echopen-foundation/echolab_box/docs/img/20190922_094147.jpg

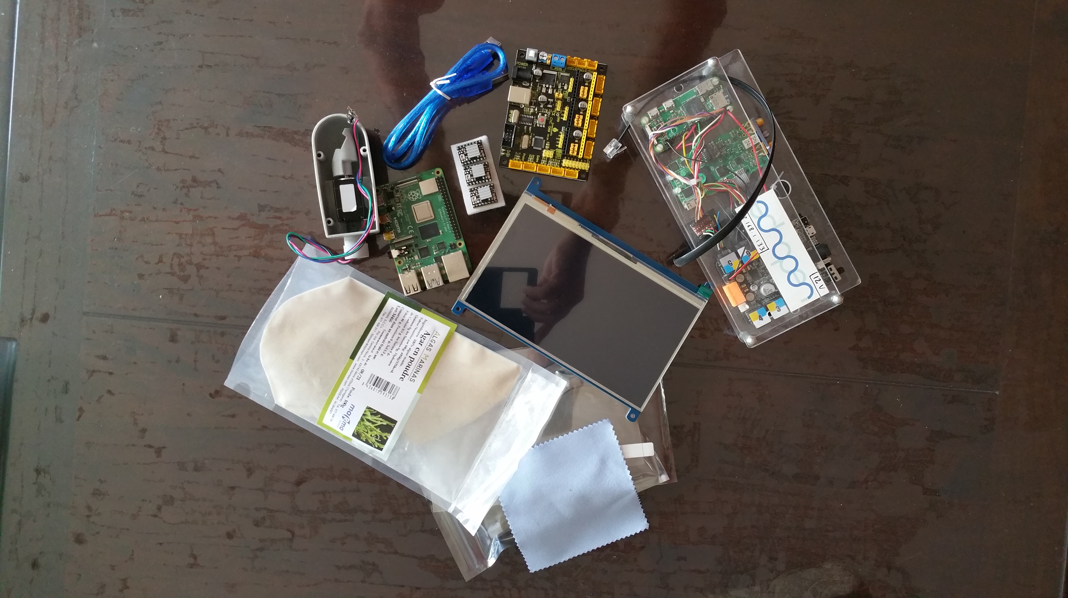
docs/img/20190922_094147.jpg
