echopen-foundation/echolab_box/docs/img/20190924_202057_2.jpg

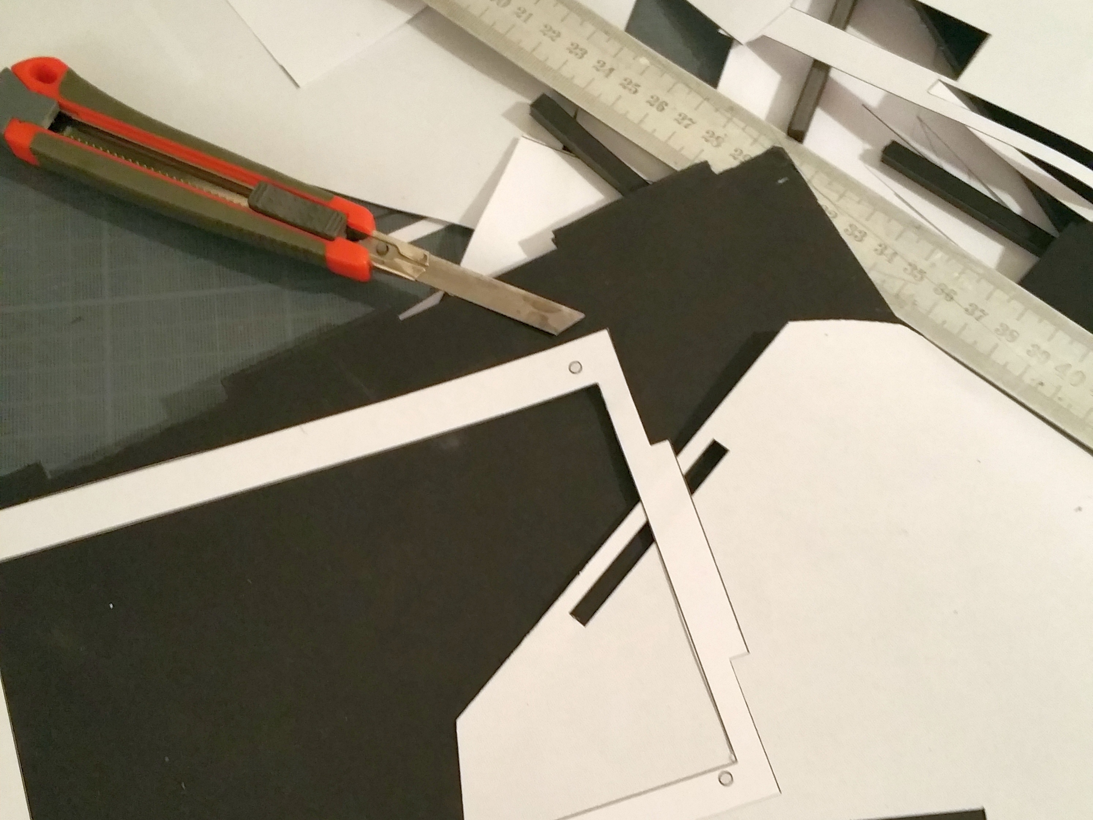
docs/img/20190924_202057_2.jpg
