echopen-foundation/echolab_box/docs/img/20190924_202208.jpg

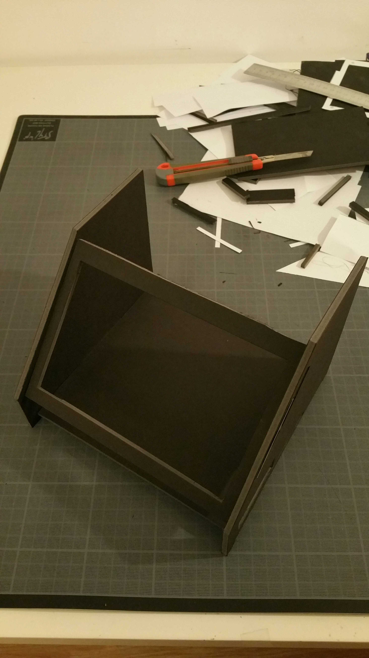
docs/img/20190924_202208.jpg
