echopen-foundation/echolab_box/docs/img/20190924_202229.jpg

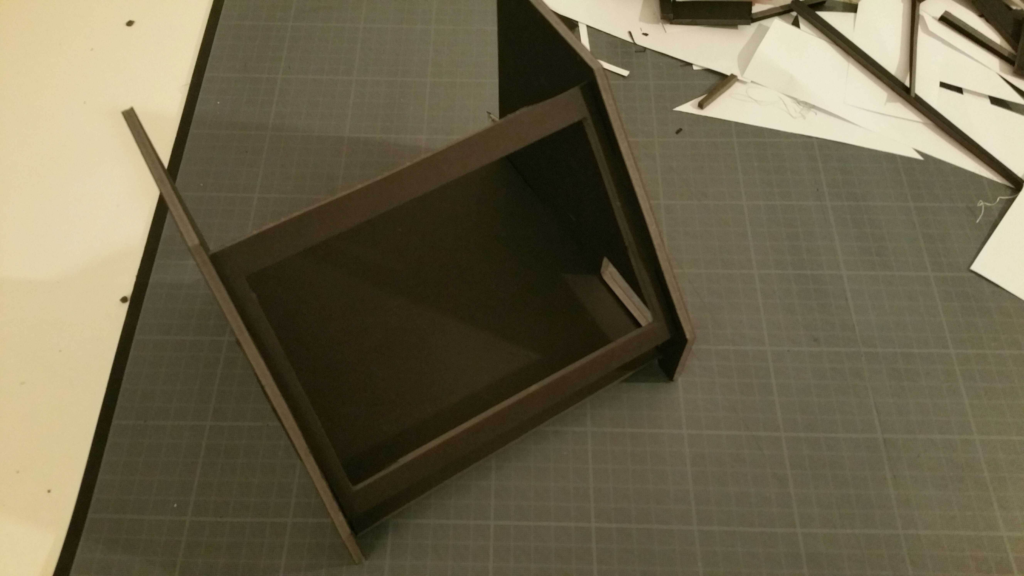
docs/img/20190924_202229.jpg
