echopen-foundation/echolab_box/docs/img/20190930_002303.jpg

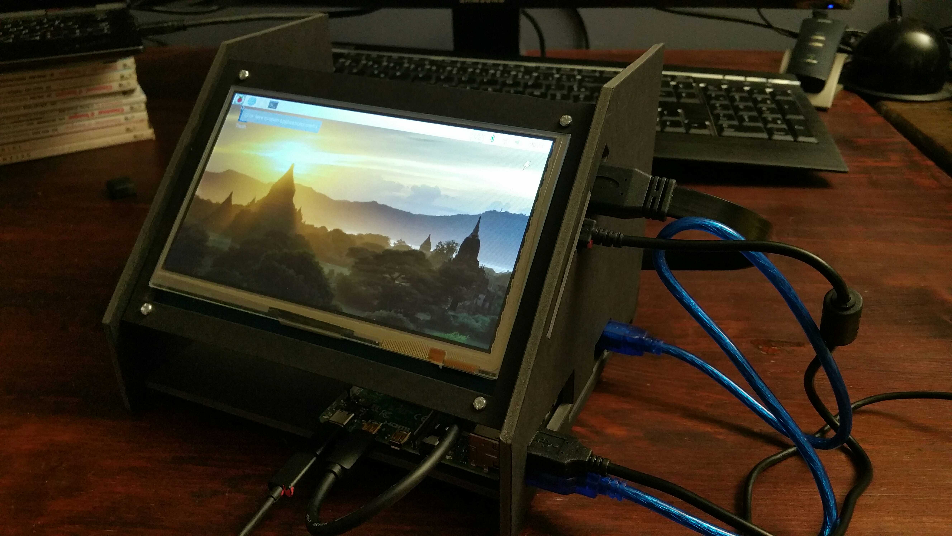
docs/img/20190930_002303.jpg
