echopen-foundation/echolab_box/docs/img/20190930_002329.jpg

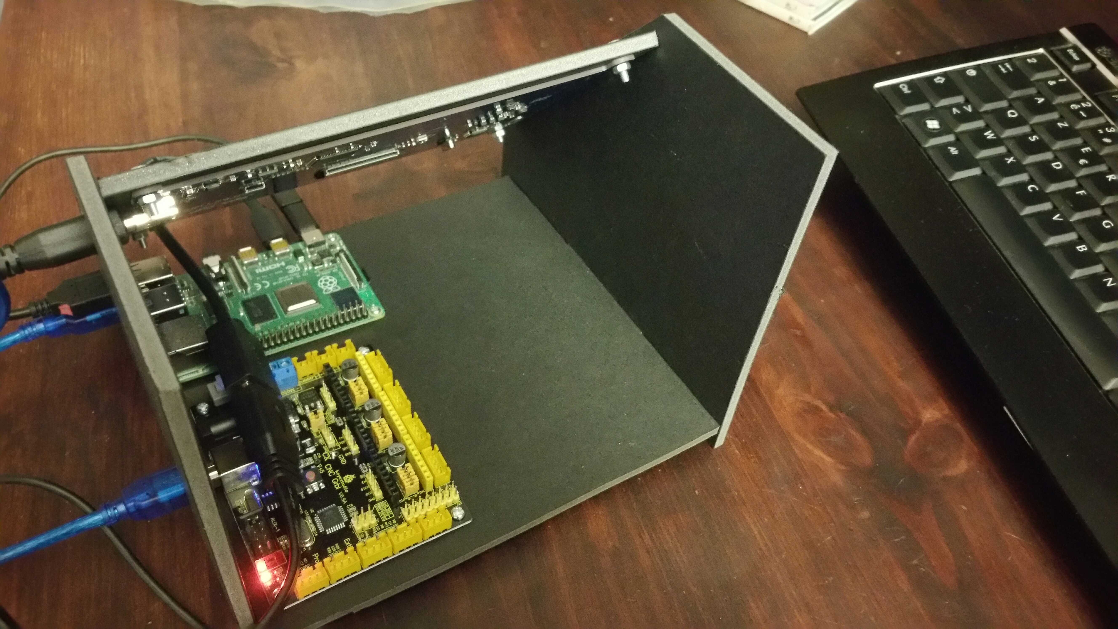
docs/img/20190930_002329.jpg
