echopen-foundation/echolab_box/docs/img/20191001_092123.jpg

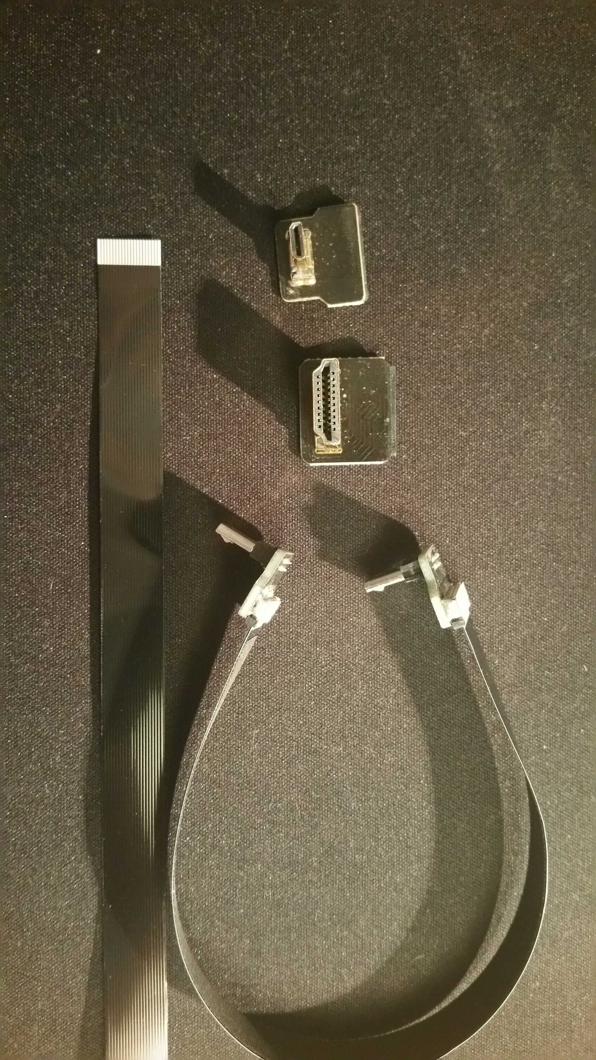
docs/img/20191001_092123.jpg
