echopen-foundation/echolab_box/docs/img/20191001_092209.jpg

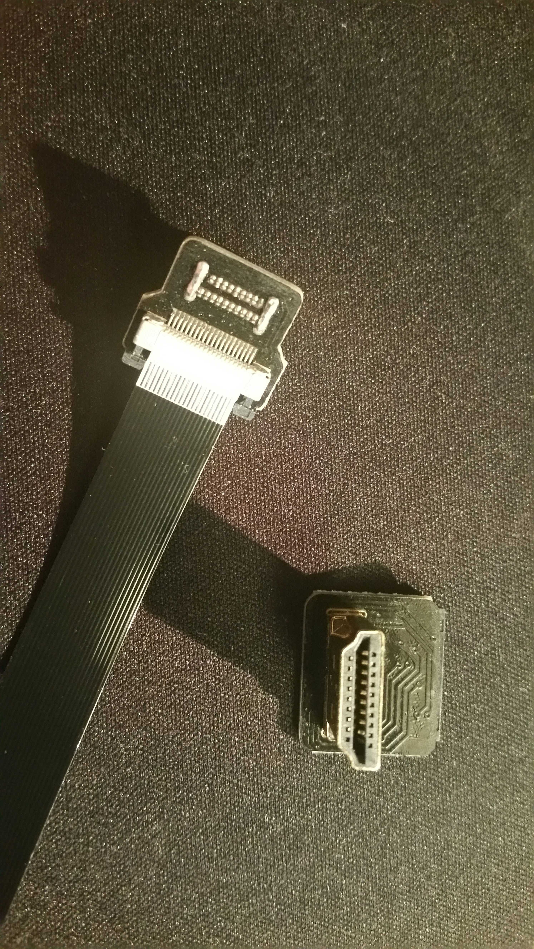
docs/img/20191001_092209.jpg
