echopen-foundation/echolab_box/docs/img/20191003_144745.jpg

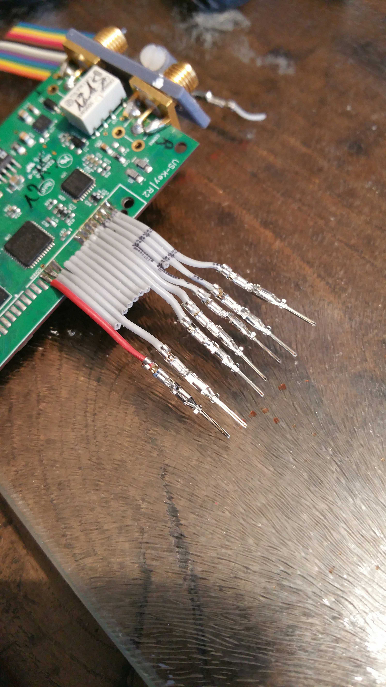
docs/img/20191003_144745.jpg
