echopen-foundation/echolab_box/docs/img/20191003_145241.jpg

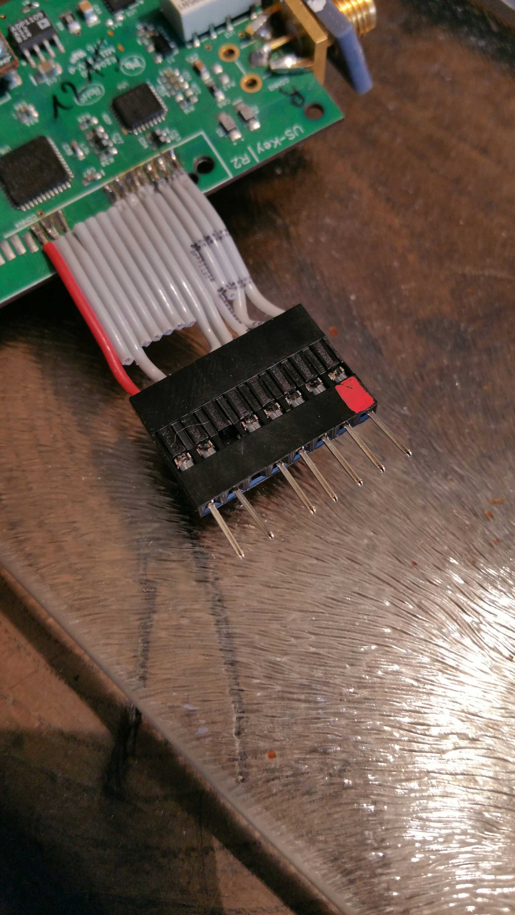
docs/img/20191003_145241.jpg
