echopen-foundation/echolab_box/docs/img/20191003_172906.jpg

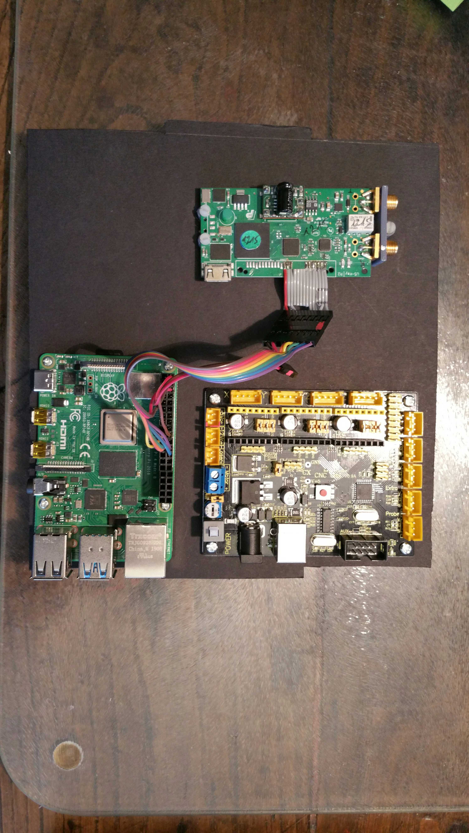
docs/img/20191003_172906.jpg
