echopen-foundation/echolab_box/docs/img/20191004_114859.jpg

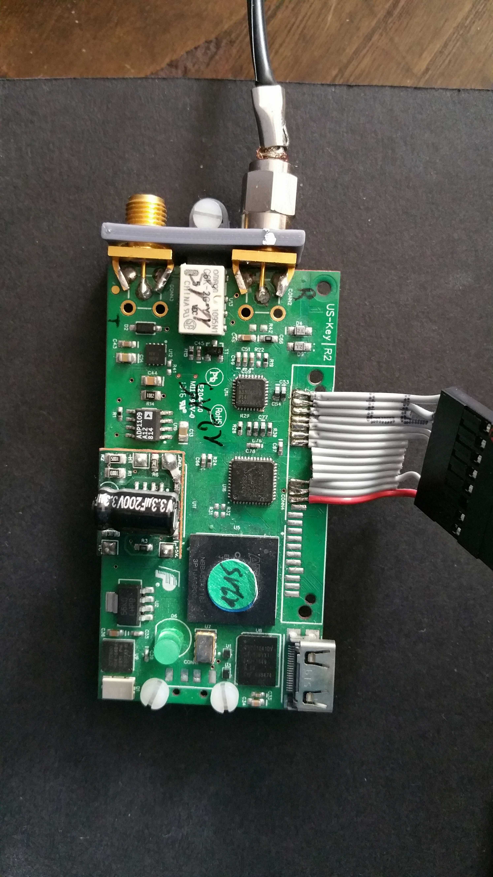
docs/img/20191004_114859.jpg
