echopen-foundation/echolab_box/docs/img/20191004_122543.jpg

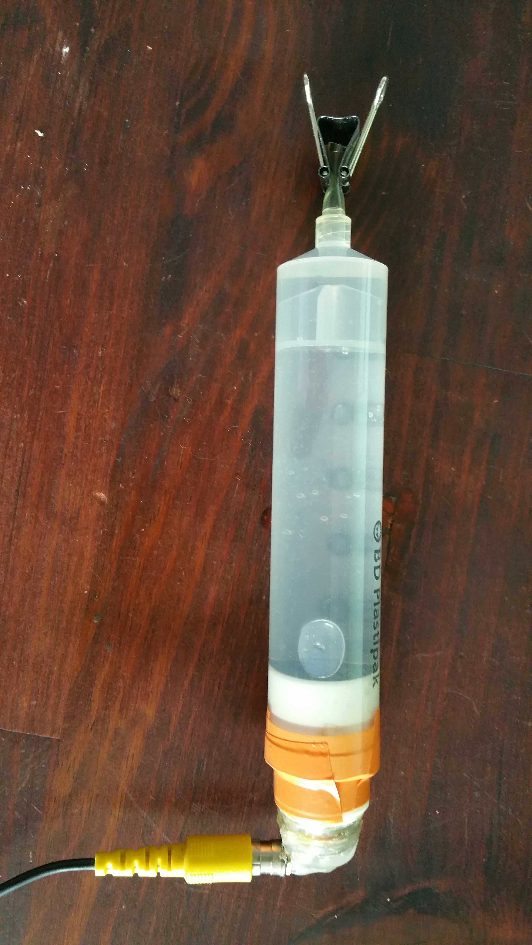
docs/img/20191004_122543.jpg
