echopen-foundation/echolab_box/docs/img/20191004_184900.jpg

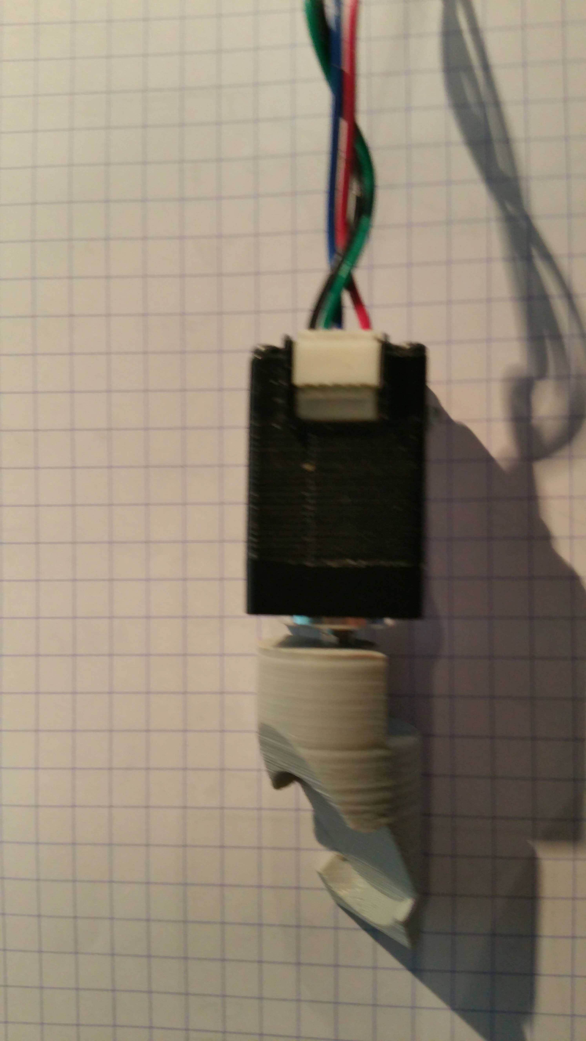
docs/img/20191004_184900.jpg
