echopen-foundation/echolab_box/docs/img/20191004_185003.jpg

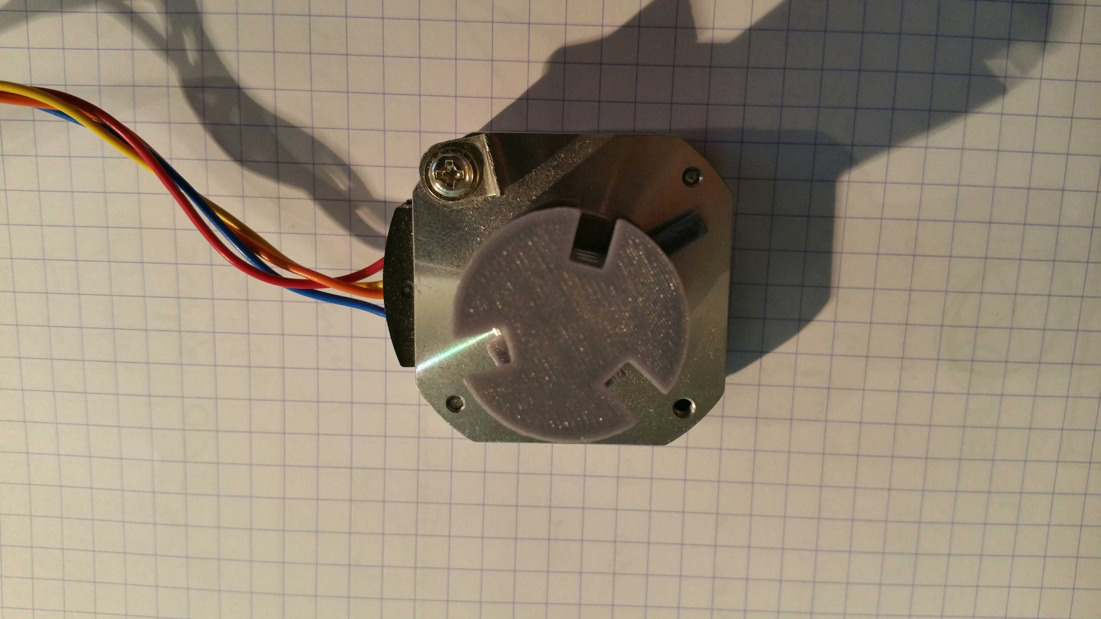
docs/img/20191004_185003.jpg
