echopen-foundation/echolab_box/docs/img/20191116_125450.jpg

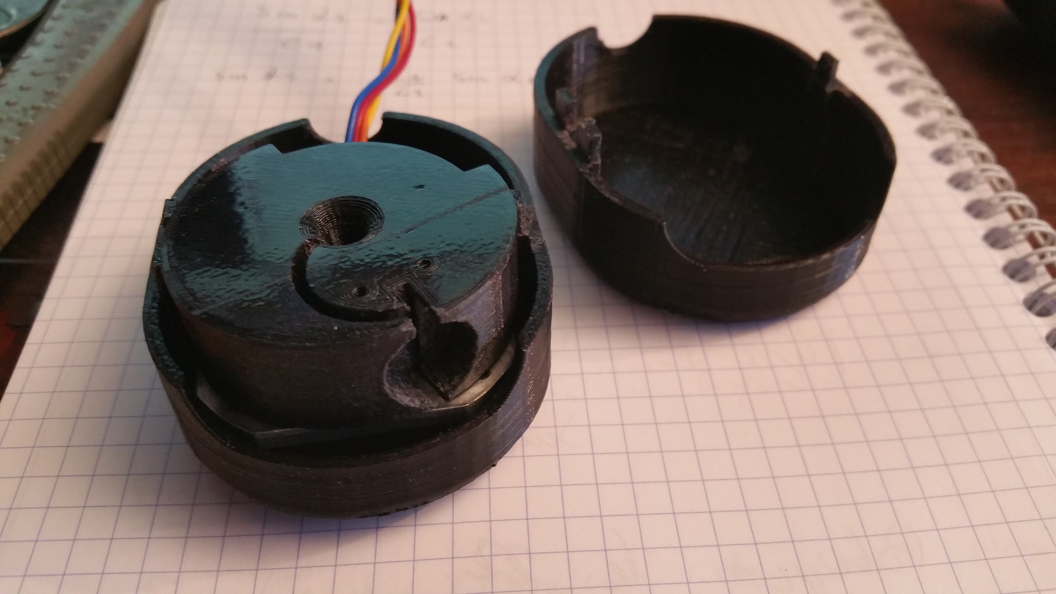
docs/img/20191116_125450.jpg
