echopen-foundation/echolab_box/docs/img/20191116_125557.jpg

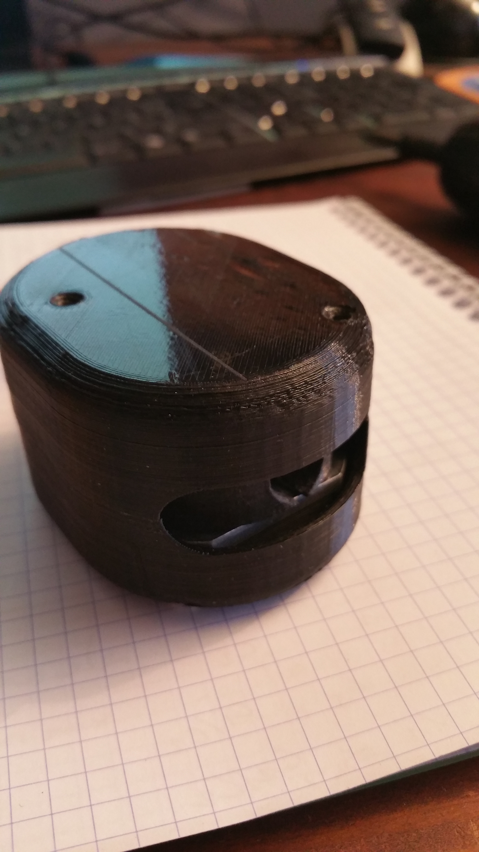
docs/img/20191116_125557.jpg
