echopen-foundation/echolab_box/docs/img/echolab_box_back.jpg

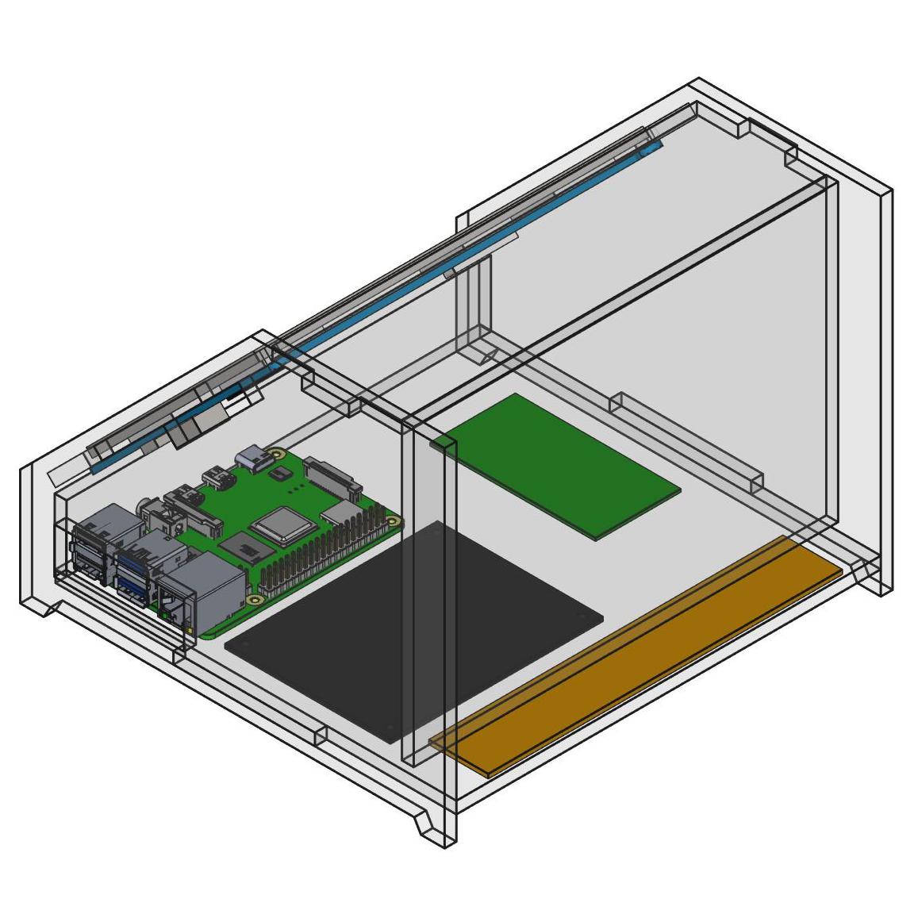
docs/img/echolab_box_back.jpg
