echopen-foundation/echolab_box/docs/img/echolab_box_front.jpg

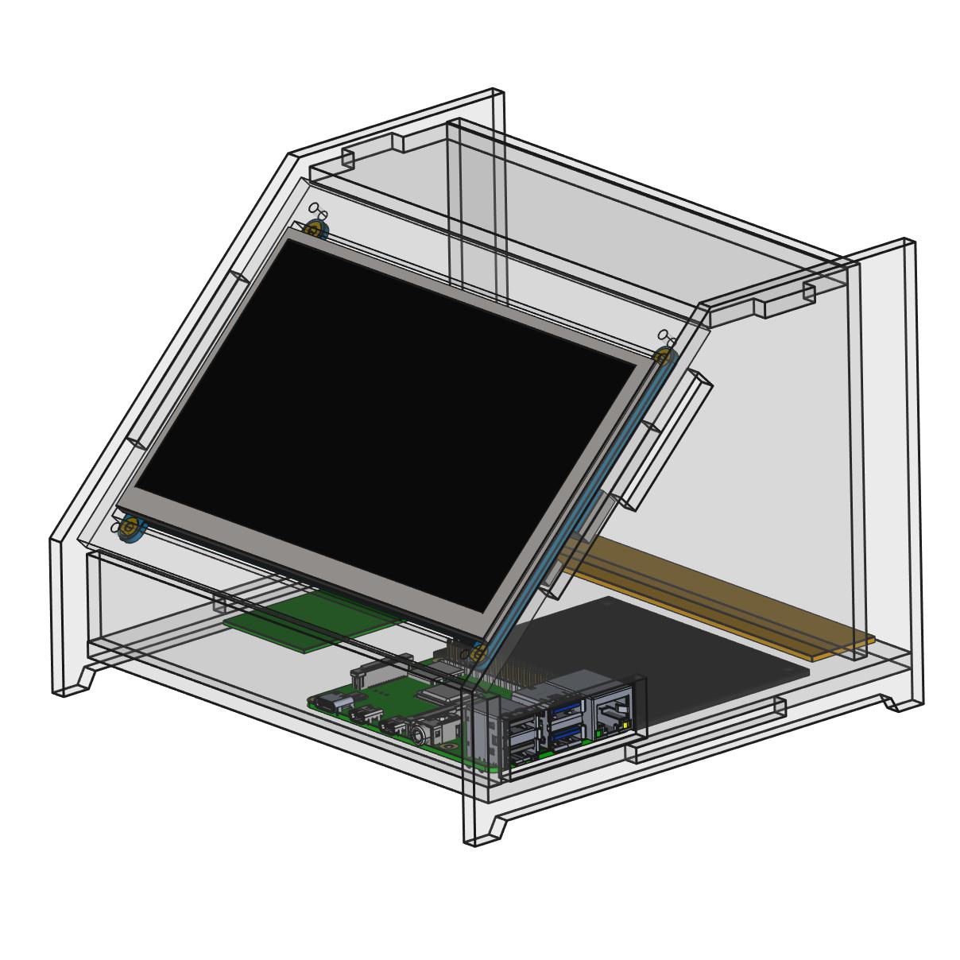
docs/img/echolab_box_front.jpg
