echopen-foundation/echolab_box/docs/img/image2.png

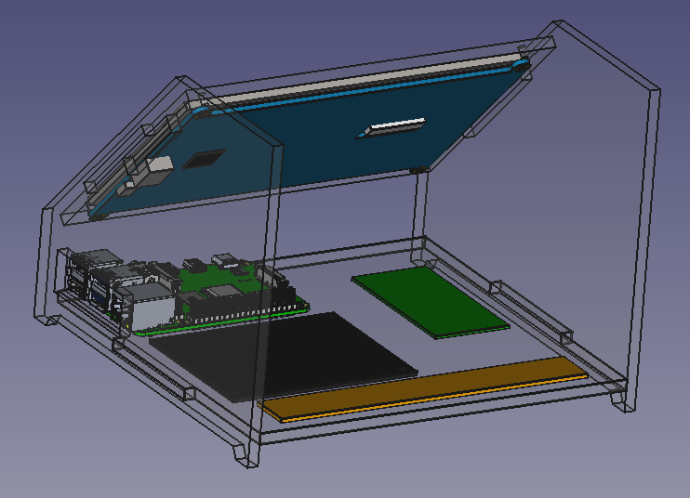
docs/img/image2.png
