echopen-foundation/echolab_box/docs/img/image.png

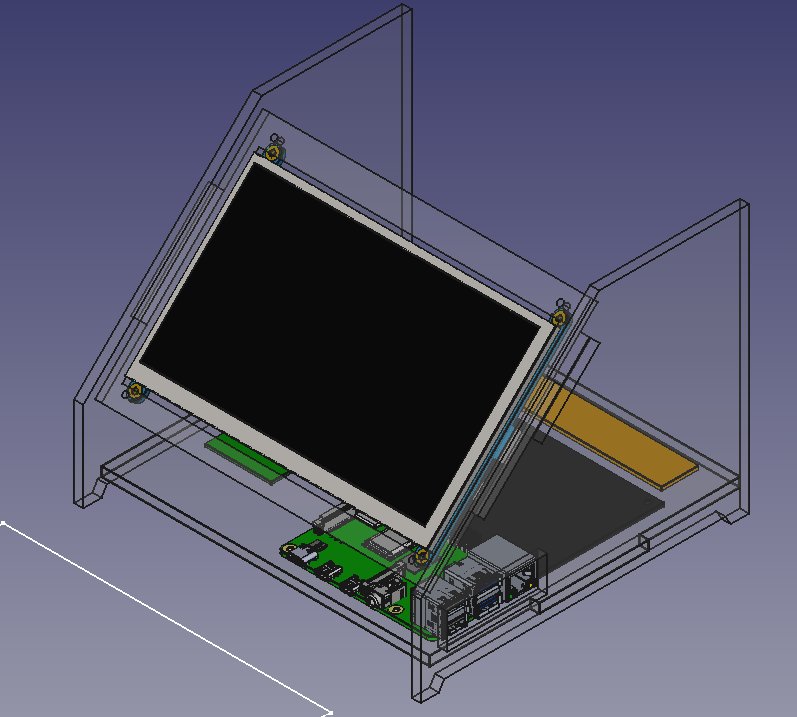
docs/img/image.png
