echopen-foundation/echolab_box/docs/img/mount_long/P1130678_tv.jpg

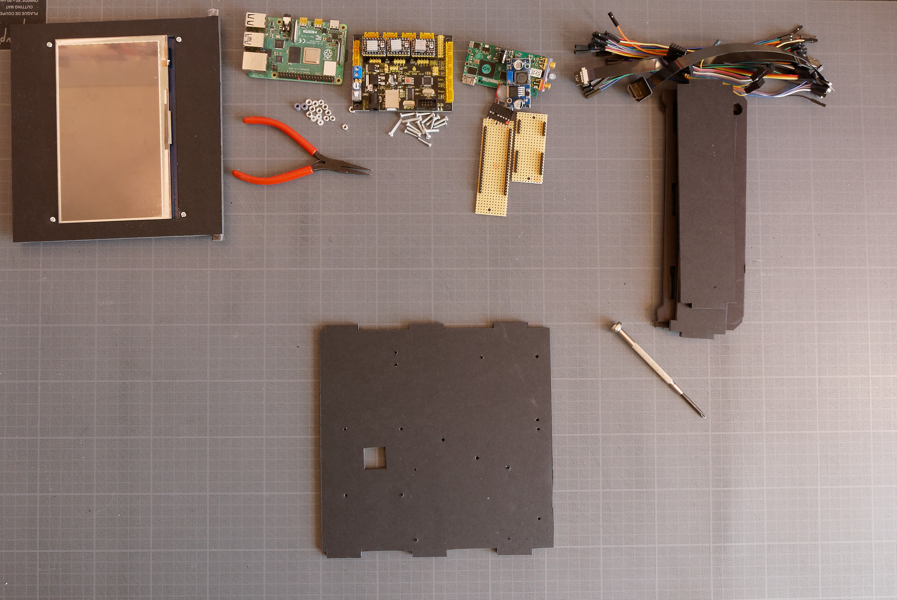
docs/img/mount_long/P1130678_tv.jpg
