echopen-foundation/echolab_box/docs/img/mount_long/P1130713_tv.jpg

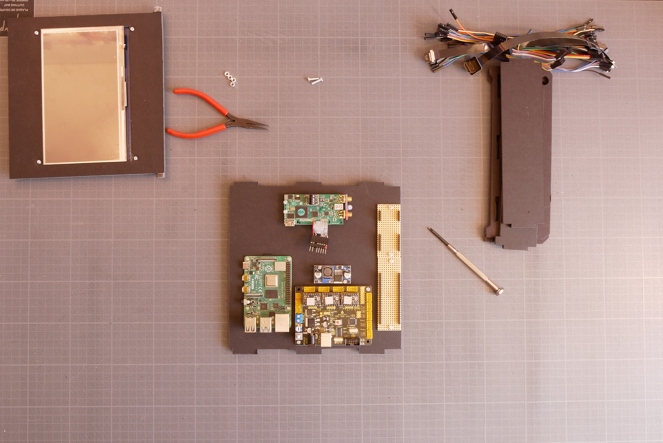
docs/img/mount_long/P1130713_tv.jpg
