echopen-foundation/echolab_box/hardware/box_block_diagram.drawio.png

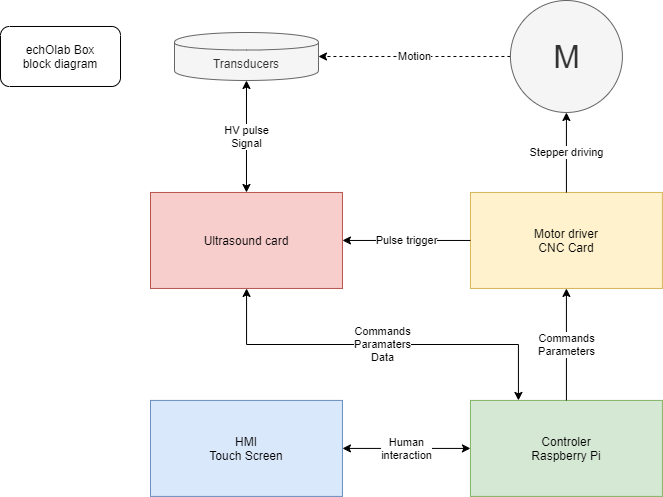
hardware/box_block_diagram.drawio.png
