echopen-foundation/echolab_box/resources/Ks0288 keyestudio/ks0288_pinout.png

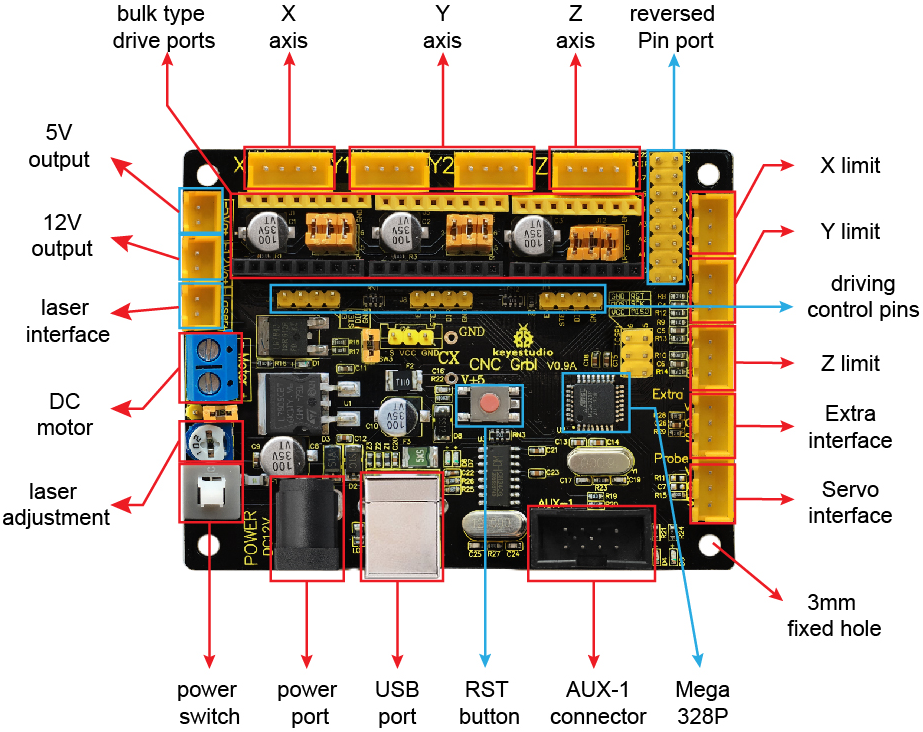
resources/Ks0288 keyestudio/ks0288_pinout.png
