echopen-foundation/echolab_box/resources/lit3rick/lit3rick.png

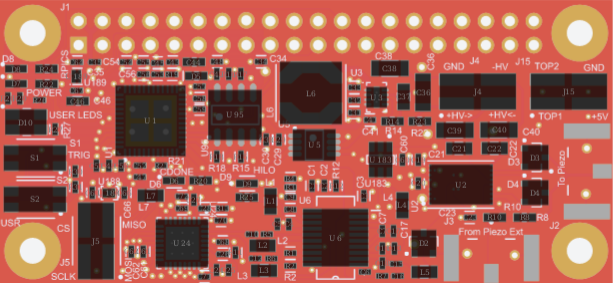
resources/lit3rick/lit3rick.png
