echopen-foundation/echolab_box/resources/lit3rick/un0rick.png

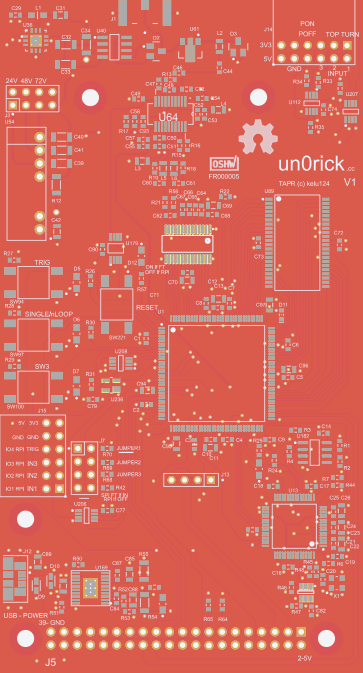
resources/lit3rick/un0rick.png
