echopen-foundation/echolab_box/resources/Raspberry Pi4/RPi_4.png

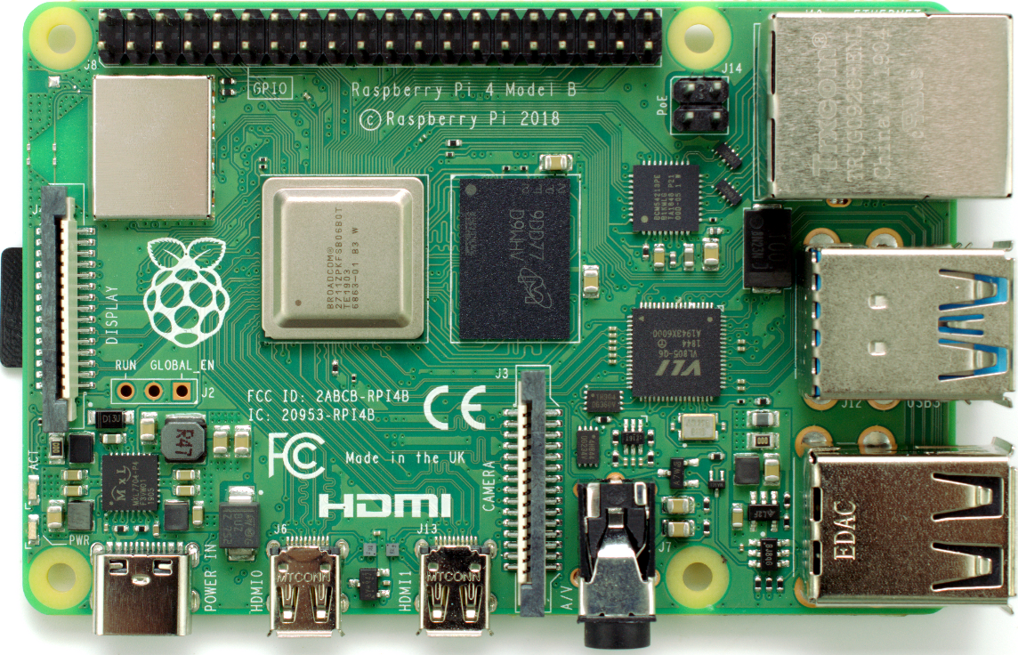
resources/Raspberry Pi4/RPi_4.png
