echopen-foundation/echolab_box/resources/Raspberry Pi4/RPi_4_pinout.png

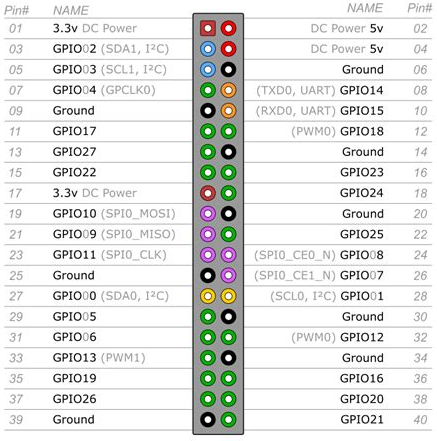
resources/Raspberry Pi4/RPi_4_pinout.png
