echopen-foundation/echolab_box/resources/us_spi/Function 9 pitchcatch 1.bmp

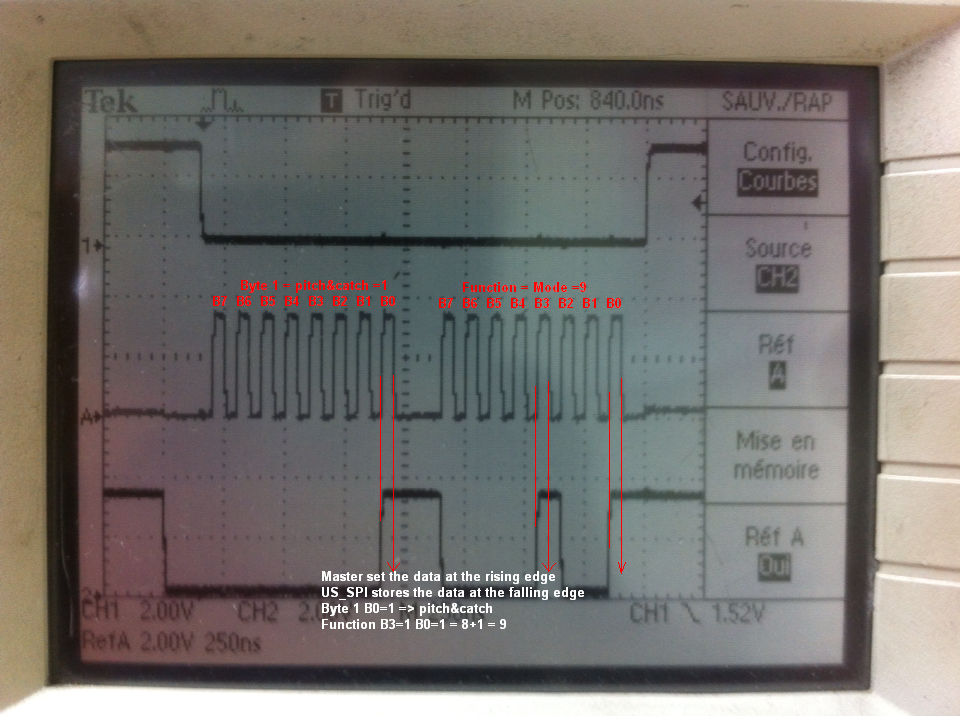
resources/us_spi/Function 9 pitchcatch 1.bmp
