echopen-foundation/echolab_box/resources/us_spi/Function 9 pulse-echo 0.bmp

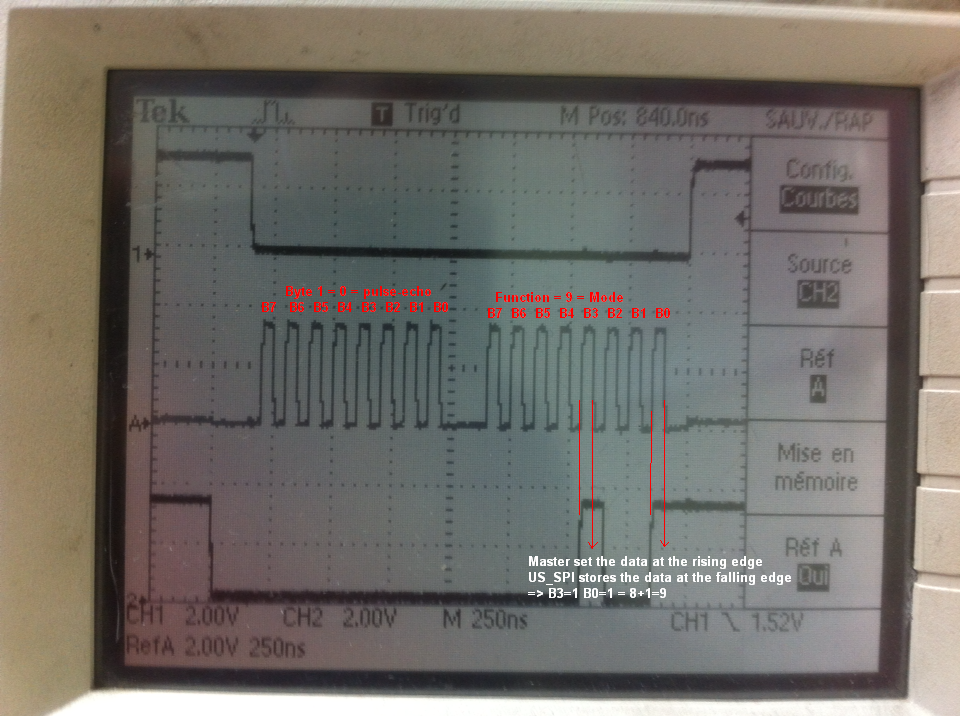
resources/us_spi/Function 9 pulse-echo 0.bmp
