echopen-foundation/echolab_box/resources/us_spi/us_spi.png

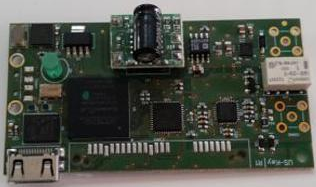
resources/us_spi/us_spi.png
