echopen-foundation/echolab_box/docs/img/mount_short/echolab_box_step_13.jpg

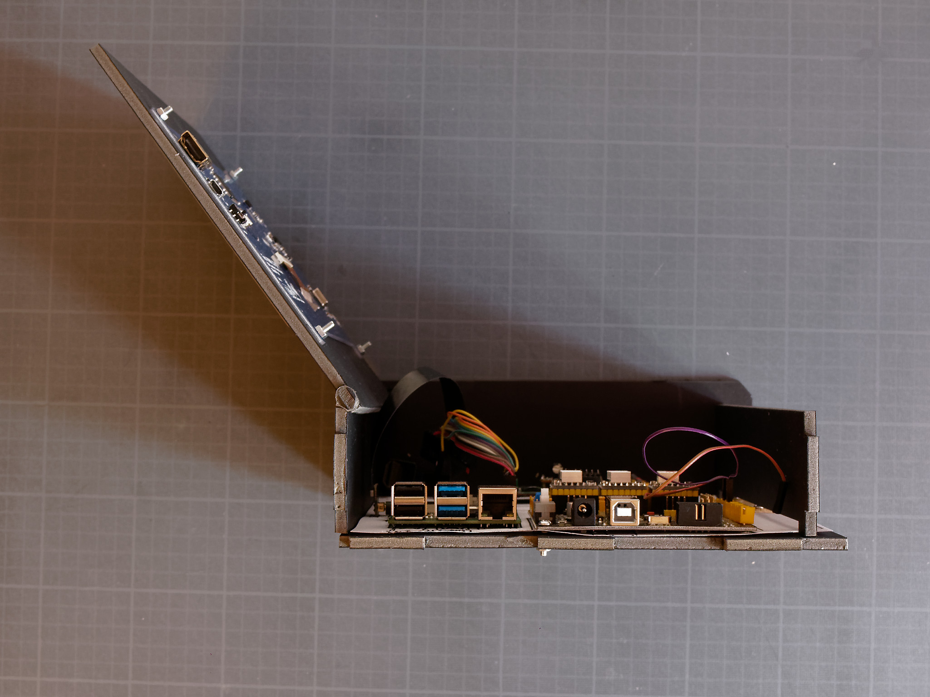
docs/img/mount_short/echolab_box_step_13.jpg
