echopen-foundation/echolab_box/hardware/box_usspi_wiring_v0.png

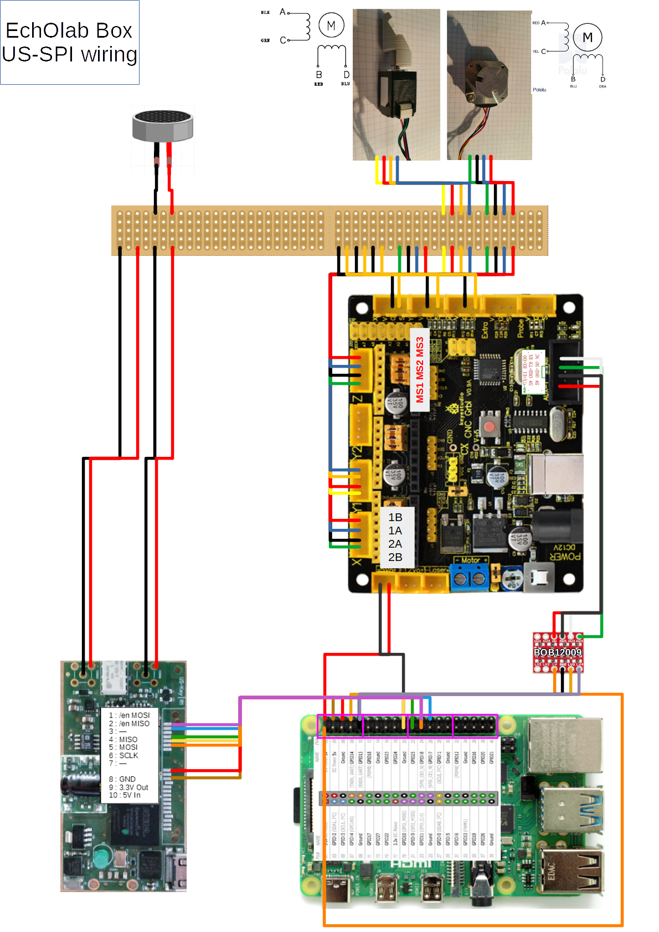
hardware/box_usspi_wiring_v0.png
