echopen-foundation/echolab_box/hardware/box_usspi_wiring_wip.drawio.png

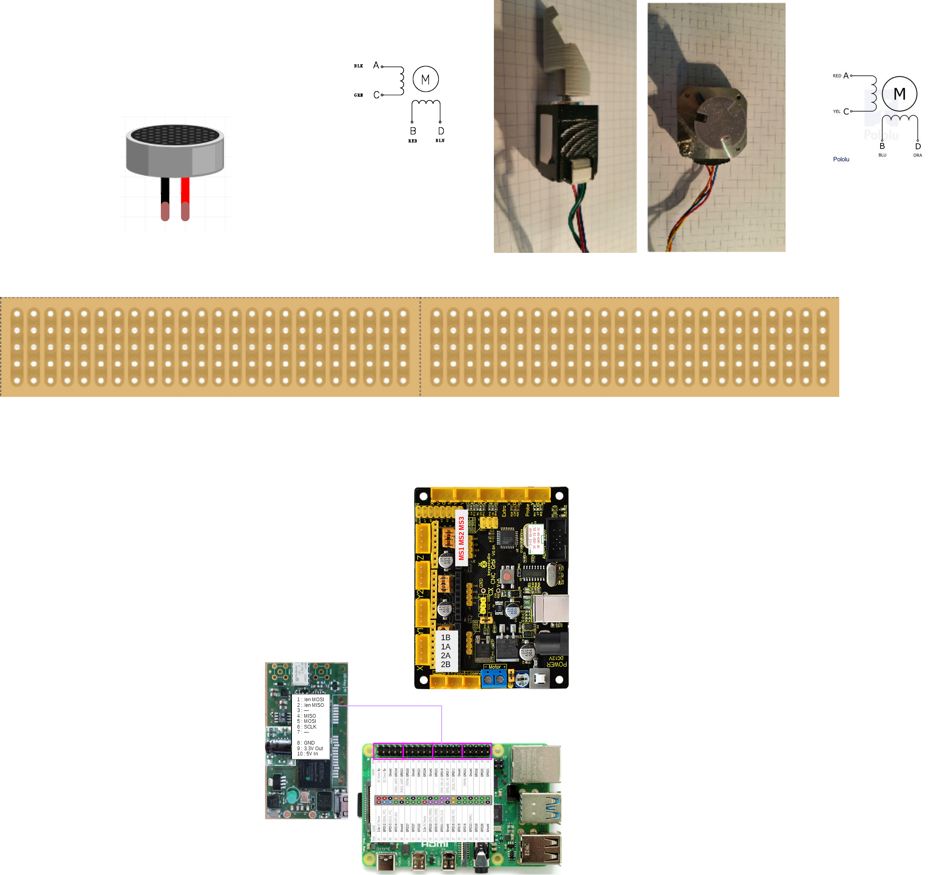
hardware/box_usspi_wiring_wip.drawio.png
