echopen-foundation/echolab_box/mechanics/build/Devis Sculpteo.png

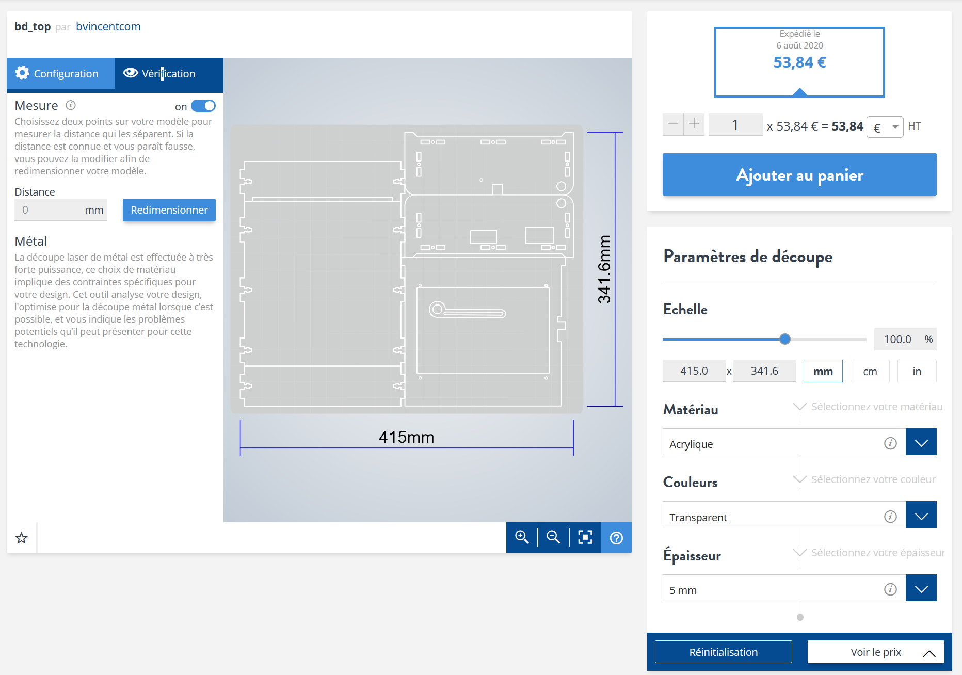
mechanics/build/Devis Sculpteo.png
