echopen-foundation/echolab_box/soft/examples/XY_table_webapp_v1/GCodeParser/GCodeParser.ino

#include <Servo.h>
// define the parameters of our machine.
float X_STEPS_PER_INCH = 192;    //org 48;
float X_STEPS_PER_MM   = 350.32; //org 40;
int X_MOTOR_STEPS      = 400;    //org 100;

float Y_STEPS_PER_INCH = 192;    //org 48;
float Y_STEPS_PER_MM   = 350.32; //org 40;
int Y_MOTOR_STEPS      = 400;    //org 100;

float Z_STEPS_PER_INCH = 48;
float Z_STEPS_PER_MM   = 40;
int Z_MOTOR_STEPS      = 100;

//our maximum feedrates
long FAST_XY_FEEDRATE = 8000; // org 2000;
long FAST_Z_FEEDRATE = 2000;

// Units in curve section
#define CURVE_SECTION_INCHES 0.019685
#define CURVE_SECTION_MM 0.5

// Set to one if sensor outputs inverting (ie: 1 means open, 0 means closed)
// RepRap opto endstops are *not* inverting.
int SENSORS_INVERTING = 1;

// How many temperature samples to take.  each sample takes about 100 usecs.


/****************************************************************************************
* digital i/o pin assignment
*
* this uses the undocumented feature of Arduino - pins 14-19 correspond to analog 0-5
****************************************************************************************/
                      // Orion update for plotter table XY
int X_STEP_PIN  = 10; // Port1_slot2 //org 8;
int X_DIR_PIN   = 11; // Port1_slot1 //org 11;
int X_ENABLE_PIN = 8; // Port4_slot1 //org 4; FAKE
int X_MIN_PIN   = A3; // Port6_slot2 //org A4;
int X_MAX_PIN   = A2; // Port6_slot1 //org A5;

int Y_STEP_PIN   = 9; // Port2_slot2 //org 12;
int Y_DIR_PIN    = 3; // Port2_slot1 //org 13;
int Y_ENABLE_PIN = 8; // Port4_slot1 //org 4; FAKE
int Y_MIN_PIN   = 13; // Port3_slot2 //org A1;
int Y_MAX_PIN   = 12; // Port3_slot1 //org A0;

int Z_STEP_PIN     = 8; // Port4_slot1 //org A3; FAKE
int Z_DIR_PIN      = 8; // Port4_slot1 //org 9; FAKE
int Z_ENABLE_PIN   = 8; // Port4_slot1 //org 4; FAKE
int Z_MIN_PIN      = 8; // Port4_slot1 //org A1; FAKE
int Z_MAX_PIN      = 8; // Port4_slot1 //org A0; FAKE
int Z_ENABLE_SERVO = 0; //org 1;
#define COMMAND_SIZE 128

char commands[COMMAND_SIZE];
byte serial_count;
int no_data = 0;

Servo servo;

int currentPosServo = 90;
int targetPosServo = 90;
bool comment = false;

//--------------------------------------------------------------------------------
void setup()
{
	//Do startup stuff here
	Serial.begin(115200);
        if(Z_ENABLE_SERVO==1){
          servo.attach(Z_STEP_PIN);
        }
	//other initialization.
	init_process_string();
	init_steppers();
	process_string("G90",3);//Absolute Position
        Serial.println("start_parser");
}

//--------------------------------------------------------------------------------
void loop()
{
  
	char c;
	//read in characters if we got them.
	if (Serial.available() > 0)
	{ c = Serial.read();
		no_data = 0;
		//newlines are ends of commands.
		if (c != '\n' && c!= '\r')
		{ if(c==0x18)
      { Serial.println("Grbl 1.0");
			}
			else
			{ if (c == '(')
        { comment = true;
        }
        // If we're not in comment mode, add it to our array.
        if (!comment)
        {  commands[serial_count] = c;
           serial_count++;
        }
        if (c == ')')
        { comment = false; // End of comment - start listening again
        }
      }	
		}
  	else
  	{ no_data++;
  		delayMicroseconds(100);
  	  //if theres a pause or we got a real command, do it   /*|| no_data > 100 */
      //if (serial_count && (c == '\n' || c == '\r'))
  	  { //process our command!
  		  process_string(commands, serial_count);
  		  //clear command.
  		  init_process_string();
  	  }
  
  	  //no data?  turn off steppers
  	  //if (no_data > 1000)
  	  //{ disable_steppers();
  	  //}
    }
	}
//        return;
//                delay(5);
//                int dPos = abs(currentPosServo-targetPosServo);
//                if(currentPosServo<targetPosServo){
//                   currentPosServo += dPos>8?6:1;
//                }else if(currentPosServo>targetPosServo){
//                   currentPosServo -= dPos>8?6:1;
//                }
                      
}
