echopen-foundation/echolab_box/docs/img/20190924_202057.jpg

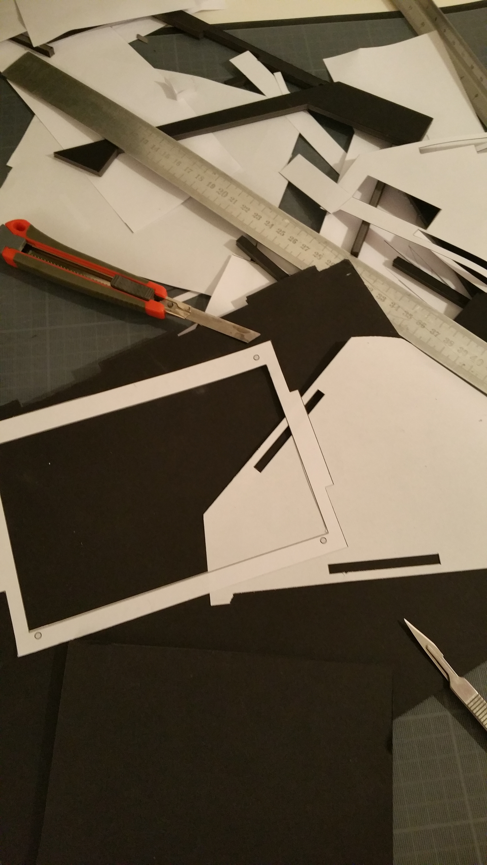
docs/img/20190924_202057.jpg
