echopen-foundation/echolab_box/docs/img/20191107_163451.jpg

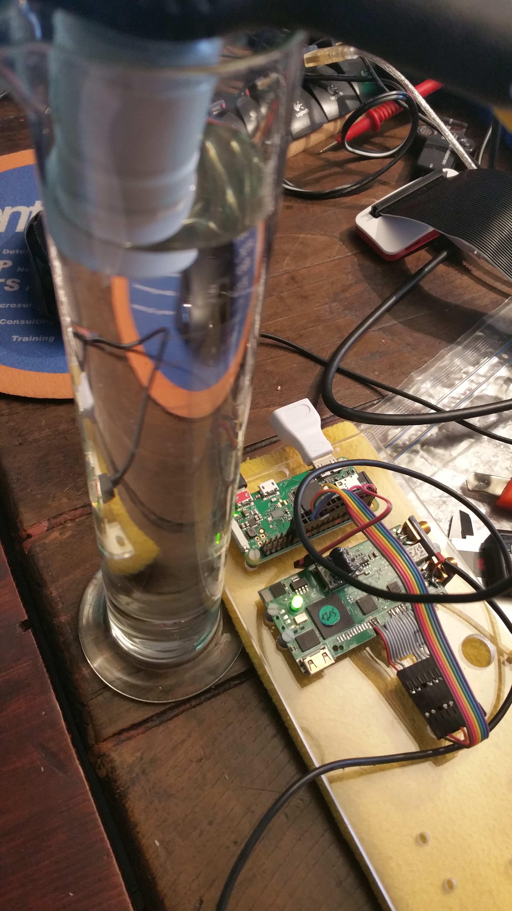
docs/img/20191107_163451.jpg
